AU199/Mecahnical_Keyboard/Images/image (1).png

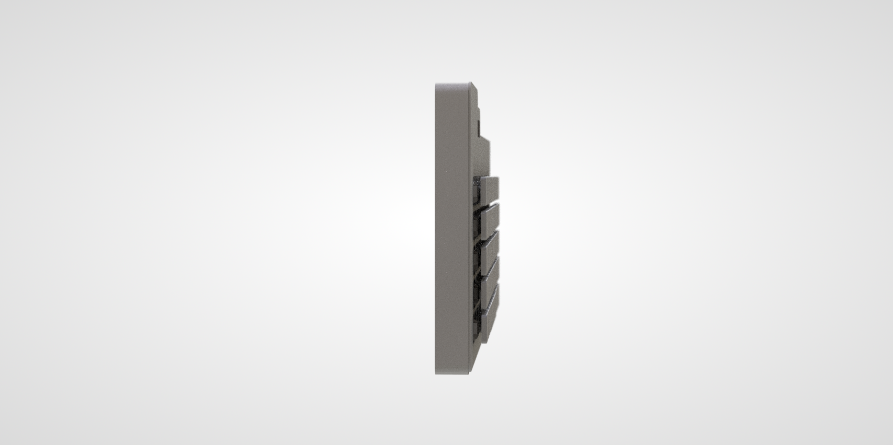
Images/image (1).png
