AU199/Mecahnical_Keyboard/Images/image (2).png

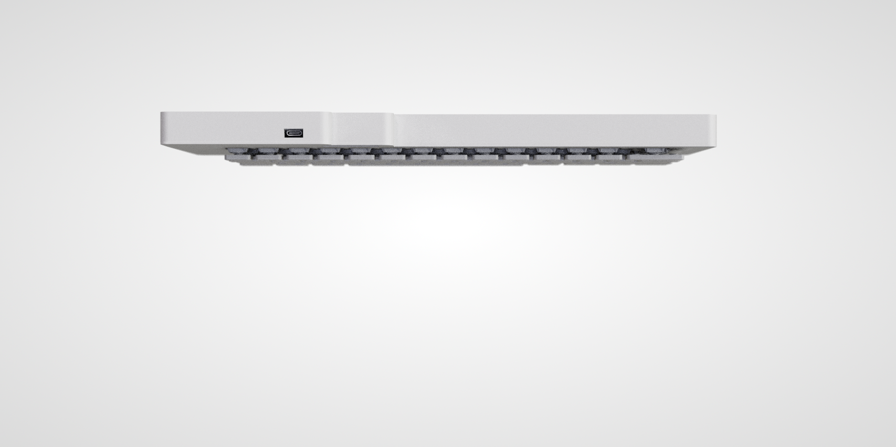
Images/image (2).png
