AU199/Mecahnical_Keyboard/Images/image (3).png

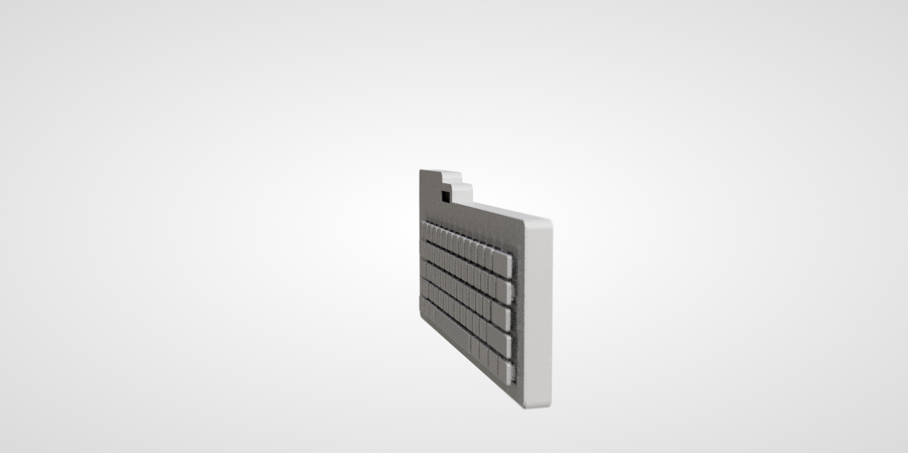
Images/image (3).png
